yroffin/grbl-cnc32/firmware/storage-ctrl.hpp

#ifndef _STORAGE_CONTROLLER_
#define _STORAGE_CONTROLLER_

#include "SD.h"
#include "utils.hpp"
#define MAXSIZE_OF_CWD 128
#define MAXSIZE_OF_ENTRY 128

class StorageEntry
{
public:
  boolean isDirectory();
  const char *getPath();
  void setDirectory(boolean value);
  void setPath(const char *path);
  void clear();

private:
  boolean dir;
  char path[MAXSIZE_OF_CWD];
};

class StorageStore
{
public:
  StorageStore();
  void clear();
  StorageEntry *get(int index);
  void addDirectory(const char *value);
  void addFile(const char *value);

  virtual int scan(const char *base) {}
  virtual int open(const char *filename) {}
  virtual boolean readline(char *buffer, int16_t maxLength) {}
  virtual void close() {}

protected:
  int16_t storageEntryCount = 0;
  StorageEntry *storageEntry[MAXSIZE_OF_ENTRY];
};

class StorageFileStore : public StorageStore
{
public:
  virtual int scan(const char *base);
  virtual int open(const char *filename);
  virtual boolean readline(char *buffer, int16_t maxLength);
  virtual void close();

private:
  char cwd[MAXSIZE_OF_CWD];
  boolean isOpen = false;
  File file;
};

class StorageCmdStore : public StorageStore
{
public:
  virtual int scan(const char *base);
  virtual int open(const char *filename);
  virtual boolean readline(char *buffer, int16_t maxLength);
  virtual void close();

private:
  char name[32];
  int offset = 0;
};

enum selector
{
  FILES,
  COMMANDS
};

class StorageCtrl
{
public:
  StorageCtrl();
  void init();

  selector files();
  selector commands();
  boolean isFiles();
  boolean isCommands();
  boolean isFile(int index);

  void remove(const char *filename);
  int touch(const char *filename, const char *data);
  int append(const char *filename, const char *data);

  int scan();
  const char *path(int index);
  int open(const char *filename);
  boolean readline(char *buffer, int16_t maxLength);
  void close();

  static StorageCtrl *instance();

protected:
  StorageFileStore fileStore;
  StorageCmdStore cmdStore;
  selector state = FILES;
};

#endif
