yroffin/grbl-cnc32/firmware/widget.hpp

#ifndef _WIDGET_TFT_
#define _WIDGET_TFT_

#include "stdio.h"
#include "vars.hpp"
#include "TFT_eSPI_ms/TFT_eSPI.h"
#include "evt-ctrl.hpp"
#include "json-config.hpp"
#include "i18n-ctrl.hpp"

#define MAXSIZE_OF_NAME 32
#define MAXSIZE_OF_LABEL 256

class TFT_Widget
{
public:
  TFT_Widget();
  const char *getKey(const char *k1, const char *k2);
  int getKeyAsInt(const char *k1, const char *k2, int def);
  virtual void notify(const Event *event);
  virtual void render();
  virtual void draw();
  virtual void show();
  virtual void hide();
  virtual void setPosition(int16_t _x, int16_t _y);
  virtual void setInvalidated(bool _active);
  virtual void setBackground(int16_t back)
  {
    this->background = back;
  }
  virtual void setLabel(const char *_label, ...);
  virtual const char *getLabel()
  {
    return this->label;
  }
  // Registry manipulation
  TFT_Widget *add(TFT_Widget *widget);

protected:
  boolean drawContour = false;

protected:
  void init(int16_t _id, const char *_label, int16_t _x, int16_t _y, int16_t _w, int16_t _h);
  I18nCtrl *i18n;
  JsonConfigCtrl *config;
  int16_t x;
  int16_t y;
  int16_t w;
  int16_t h;
  int16_t id;
  // Colors
  int background = TFT_BLACK;
  int selectedBackground = TFT_WHITE;
  int fontNormal = TFT_WHITE;
  int fontSelected = TFT_BLACK;
  int border = TFT_DARKGREY;
  // Fields
  char name[MAXSIZE_OF_NAME];
  char label[MAXSIZE_OF_LABEL];
  bool visible = false;
  bool invalidated = true;
  // child
  TFT_Widget *children[64];
  int8_t child = 0;
  TFT_eSPI *tft;
};

class TFT_Layer : public TFT_Widget
{
public:
  TFT_Layer(int16_t _id, int16_t _x, int16_t _y, int16_t _w, int16_t _h);

private:
};

enum ButtonState
{
  on,
  off
};

class TFT_Button : public TFT_Widget
{
public:
  TFT_Button(int16_t _id, const char *_label, int16_t _x, int16_t _y, int16_t _w, int16_t _h);
  virtual void notify(const Event *event);
  virtual void draw();
  void setEvent(EventType event);

protected:
  ButtonState state = off;
  EventType eventType = BUTTON_DOWN;
};

class TFT_ButtonCmd : public TFT_Button
{
public:
  TFT_ButtonCmd(int16_t _id, const char *_label, int16_t _x, int16_t _y, int16_t _w, int16_t _h);
  virtual void notify(const Event *event);

protected:
};

enum JOG_WAY
{
  JOG_XP,
  JOG_XM,
  JOG_YP,
  JOG_YM,
  JOG_ZP,
  JOG_ZM
};

class TFT_ButtonJog : public TFT_Button
{
public:
  TFT_ButtonJog(int16_t _id, const char *_label, JOG_WAY _jw, int16_t _x, int16_t _y, int16_t _w, int16_t _h);
  virtual void notify(const Event *event);

private:
  JOG_WAY jw;
  float xyzJogPas = 0.1;
};

class TFT_File : public TFT_Button
{
public:
  TFT_File(int16_t _id, const char *_label, int16_t _x, int16_t _y, int16_t _w, int16_t _h, boolean _align);
  virtual void draw();

private:
  boolean align;
};

class TFT_Joystick : public TFT_Widget
{
public:
  TFT_Joystick(int16_t _id, const char *_label, int16_t _x, int16_t _y, int16_t _w, int16_t _h);
  virtual void notify(const Event *event);

private:
  TFT_Button *xleft;
  TFT_Button *xright;
  TFT_Button *yup;
  TFT_Button *ydown;
  TFT_Button *zup;
  TFT_Button *zdown;
  TFT_Button *pas;
};

class TFT_Group : public TFT_Widget
{
public:
  TFT_Group(int16_t _id, const char *_label, int16_t _x, int16_t _y, int16_t _w, int16_t _h);

private:
};

class TFT_Label : public TFT_Widget
{
public:
  TFT_Label(int16_t _id, const char *_label, int16_t _x, int16_t _y);
  virtual void draw();

private:
};

class TFT_StatusBar : public TFT_Widget
{
public:
  TFT_StatusBar(int16_t _id, int16_t _x, int16_t _y);
  virtual void draw();

  void notifyWrite(uint16_t sz);
  void notifyBusy(boolean _busyState);
  void notifyWifiStatus(const char *status);
  void notifyPrintStatus(boolean isPrinting, int printed, int toPrint);

private:
  boolean busyState = true;
  // timers
  long lastWrite = 0;
  long lastBusyWrite = 0;
  // bytes counter
  uint16_t lastWriteSize = 0;
  uint16_t writeSpeed = 0;
  uint16_t write = 0;
  char wifiStatus[21];
  const char *writeStatus = "!/-\\";
  boolean isPrinting;
  int printed = 0;
  int toPrint = 0;
  // Colors
  int busyStateFgColor;
  int busyStateBgColor;
  int busyStateBgColorWarn;
  int writeStatusFgColor;
  int writeStatusBgColor;
  int writeStatusBgColorWarn;
};

class TFT_Console : public TFT_Widget
{
public:
  TFT_Console(int16_t _id, const char *_label, int16_t _sz, int16_t _x, int16_t _y, int16_t _w, int16_t _h);
  void write(const char *message);

private:
  TFT_Label *lines[16];
  int16_t sz;
};

class TFT_FileGrid : public TFT_Widget
{
public:
  TFT_FileGrid(int16_t _id, const char *_label, int16_t _x, int16_t _y, int16_t _w, int16_t _h);
  virtual void notify(const Event *event);

  virtual void onRight()
  {
    this->offset++;
    if (this->offset > this->count)
    {
      this->offset = this->count - 1;
    }
    this->refresh();
  }
  virtual void onLeft()
  {
    this->offset--;
    if (this->offset < 0)
    {
      this->offset = 0;
    }
    this->refresh();
  }

  void clear();
  void set(int16_t index, const char *label);
  virtual void refresh() {}

public:
  int16_t offset = 0;
  int16_t count = 0;
  int16_t maxLines = 5;

protected:
  TFT_Button *left;
  TFT_File *lines[5];
  TFT_Button *right;
};

#endif
