yroffin/grbl-cnc32/firmware/json-config.cpp

#include "json-config.hpp"
#include "ui.hpp"
#include "vars.hpp"

// I18nCtrl controller
JsonConfigCtrl *__instance_json_config = 0;

// singleton
JsonConfigCtrl *JsonConfigCtrl::instance()
{
  if (__instance_json_config == 0)
  {
    __instance_json_config = new JsonConfigCtrl();
  }
  return __instance_json_config;
}

// Allocate a temporary JsonDocument
// Don't forget to change the capacity to match your requirements.
// Use arduinojson.org/v6/assistant to compute the capacity.
DynamicJsonDocument config(JSON_CONFIG_SIZE);

JsonConfigCtrl::JsonConfigCtrl() : JsonStore(config)
{
}

void JsonConfigCtrl::setup()
{
  // Initialize SD library
  while (!SD.begin(SD_CHIPSELECT_PIN))
  {
    TFT_Screen::instance()->console("Waiting for SD card ...");
    delay(1000);
  }

  // load global configuration
  this->load("/config.json");

  // fix language
  strcpy(this->lang, this->getAsString("sys", "lang", "/i18n_enUS.json"));
}

void JsonConfigCtrl::write()
{
  this->save("/config.json", "/config.bak");
}
